Brasletti/Stealthmax_V2/Printable_Files/0_Chamber_Side_Mounting/CPAP_Intakes/CPAP_Tube_2020_Extrusion_Mount.stl

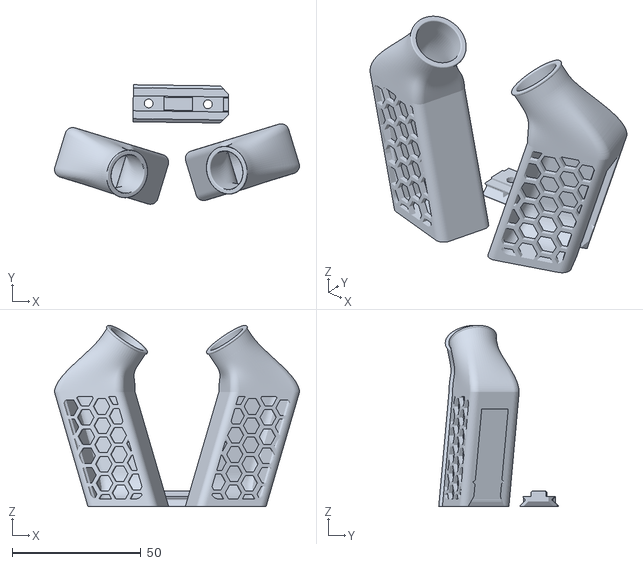
[picture p17: CAD file, 2025-04-10]
Printable_Files/0_Chamber_Side_Mounting/CPAP_Intakes/CPAP_Tube_2020_Extrusion_Mount.stl
95.1 x 46.4 x 70.4
