Brasletti/Stealthmax_V2/Printable_Files/1_Flow_Chamber/Bottom_Port_Options/5p_Microfit.step

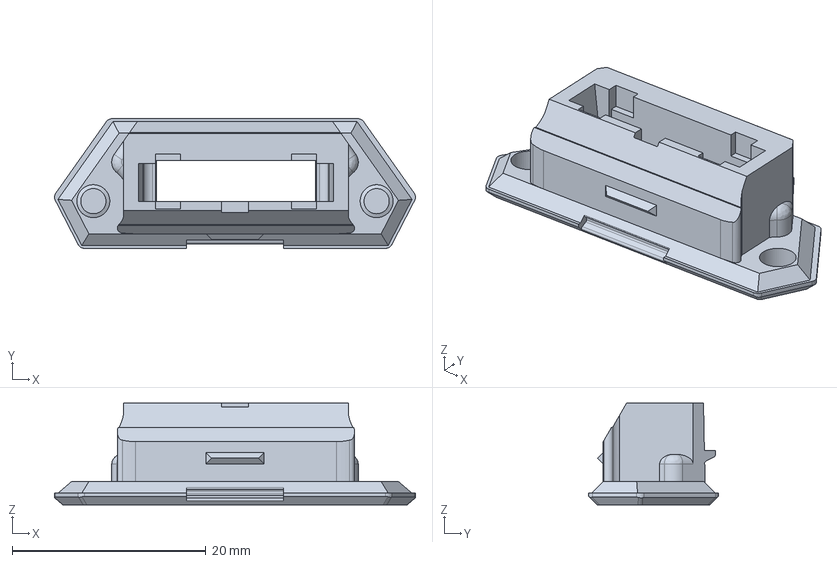
[picture p18: CAD file, 2025-04-05]
Printable_Files/1_Flow_Chamber/Bottom_Port_Options/5p_Microfit.step
37.2 x 13.4 x 10.5 mm
