Brasletti/Stealthmax_V2/Printable_Files/1_Flow_Chamber/Bowden_Tube_Intake_Options/Right/[RIGHT]Low_Blank_noLED_High_M6_PC4.step

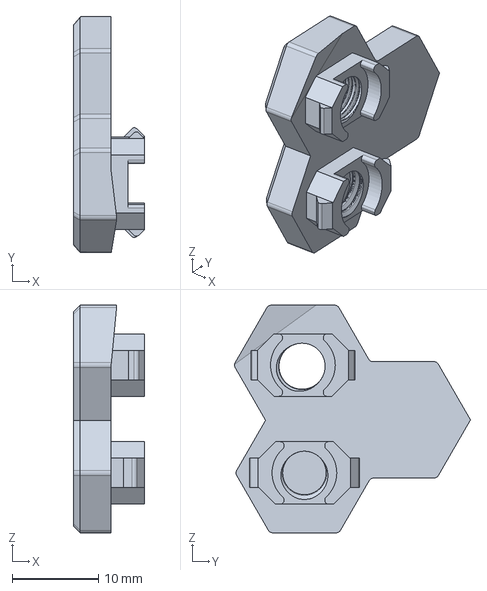
[picture p19: CAD file, 2025-04-05]
Printable_Files/1_Flow_Chamber/Bowden_Tube_Intake_Options/Right/[RIGHT]Low_Blank_noLED_High_M6_PC4.step
8.20 x 27.3 x 26.4 mm
