Brasletti/Stealthmax_V2/Printable_Files/1_Flow_Chamber/Bowden_Tube_Intake_Options/Standard_with_Single_PC6_Coupler.stl

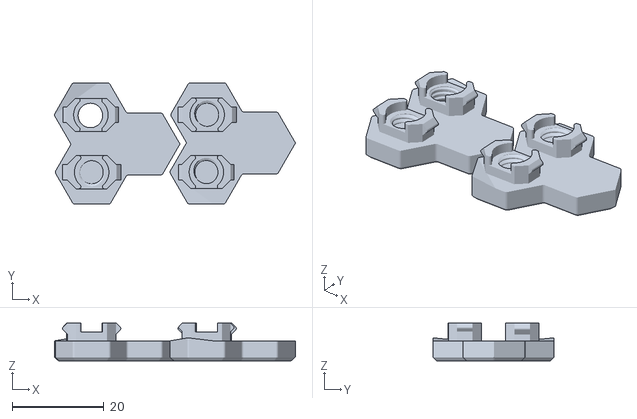
[picture p20: CAD file, 2025-03-30]
Printable_Files/1_Flow_Chamber/Bowden_Tube_Intake_Options/Standard_with_Single_PC6_Coupler.stl
52.5 x 26.4 x 8.20
