Brasletti/Stealthmax_V2/Printable_Files/0_Chamber_Side_Mounting/CPAP_Intakes/22mm_CPAP_Tube(LastZeanon)).step

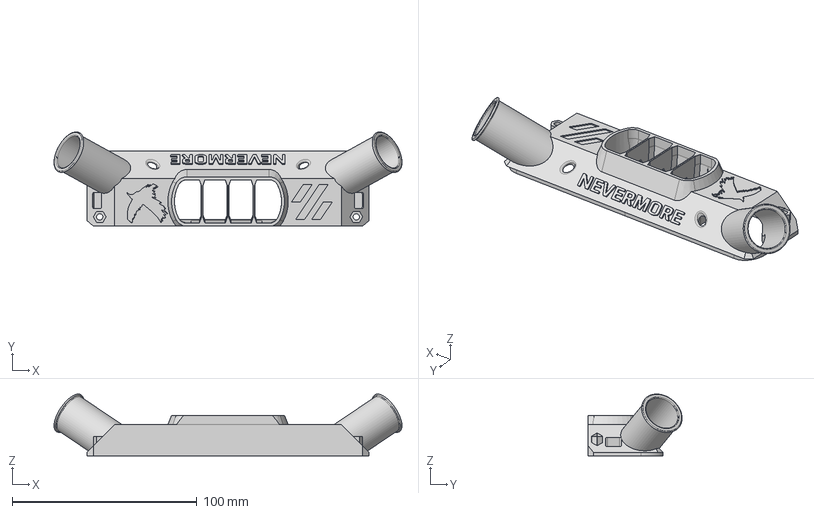
[picture p21: CAD file, 2025-04-05]
Printable_Files/0_Chamber_Side_Mounting/CPAP_Intakes/22mm_CPAP_Tube(LastZeanon)).step
188.4 x 51.0 x 33.5 mm
