Brasletti/Stealthmax_V2/Printable_Files/1_Flow_Chamber/Bottom_Port_Options/3p_Microfit.step

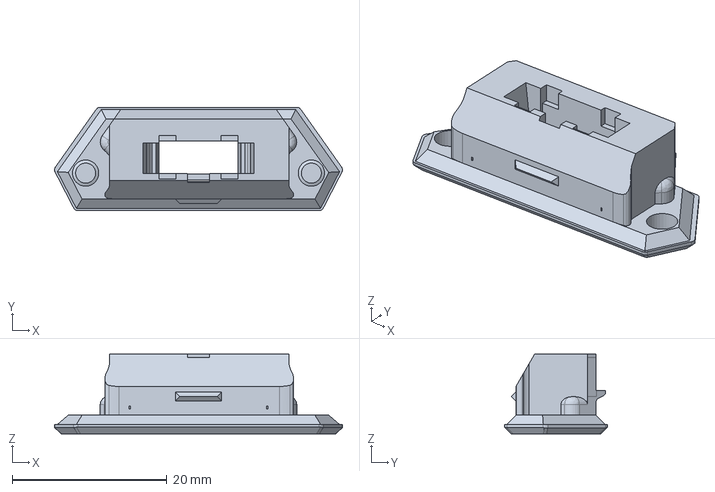
[picture p22: CAD file, 2025-04-05]
Printable_Files/1_Flow_Chamber/Bottom_Port_Options/3p_Microfit.step
37.3 x 13.4 x 10.3 mm
