Brasletti/Stealthmax_V2/Printable_Files/1_Flow_Chamber/Bottom_Port_Options/PC6_Bottom_Bowden.step

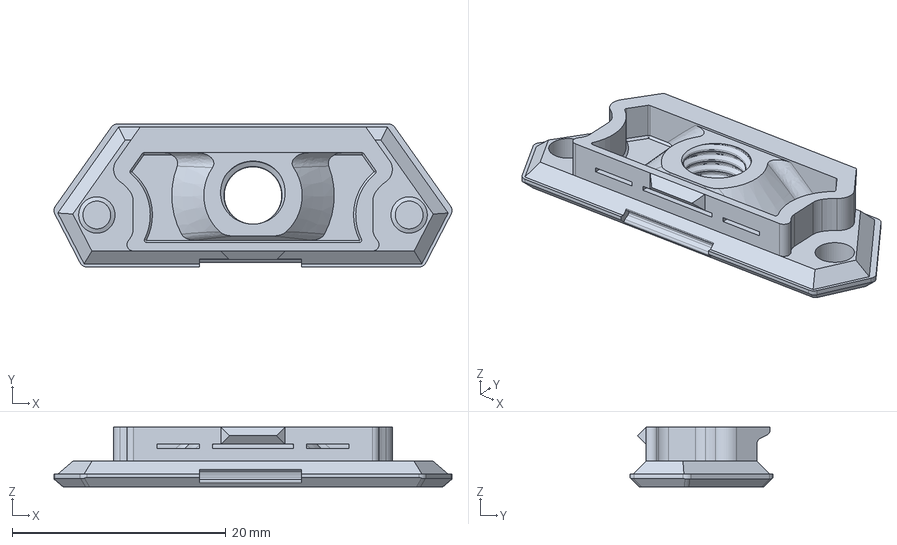
[picture p23: CAD file, 2025-04-05]
Printable_Files/1_Flow_Chamber/Bottom_Port_Options/PC6_Bottom_Bowden.step
37.2 x 13.4 x 5.61 mm
