Brasletti/Stealthmax_V2/Printable_Files/1_Flow_Chamber/Bottom_Port_Options/22mm_ID_CPAP_intake_tube.step

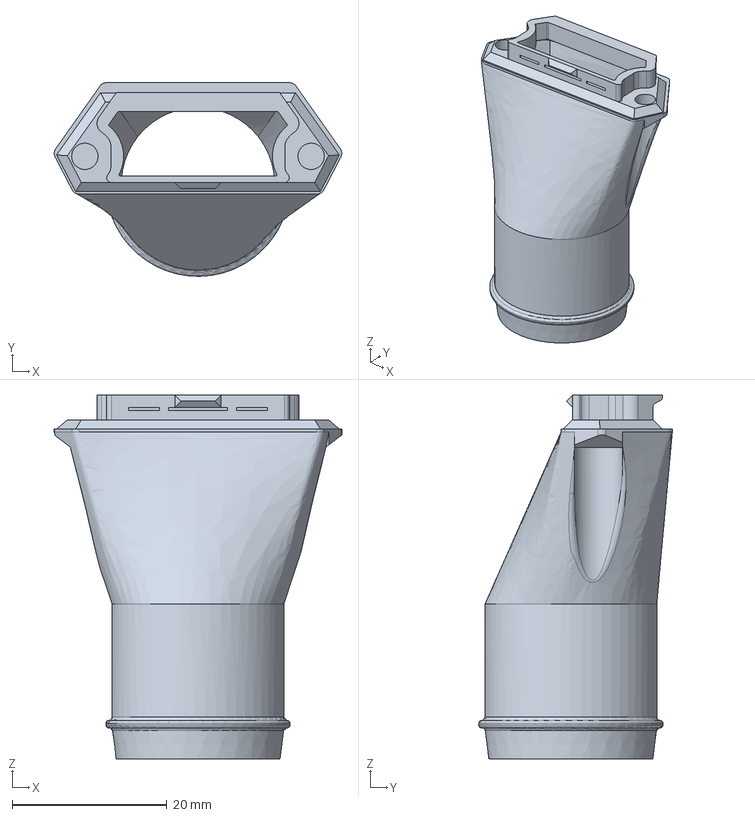
[picture p25: CAD file, 2025-04-05]
Printable_Files/1_Flow_Chamber/Bottom_Port_Options/22mm_ID_CPAP_intake_tube.step
37.1 x 25.0 x 47.0 mm
