Brasletti/Stealthmax_V2/Printable_Files/1_Flow_Chamber/Bowden_Tube_Intake_Options/Right/[RIGHT]Low_M6_PC4_LED_High_M6_PC4.step

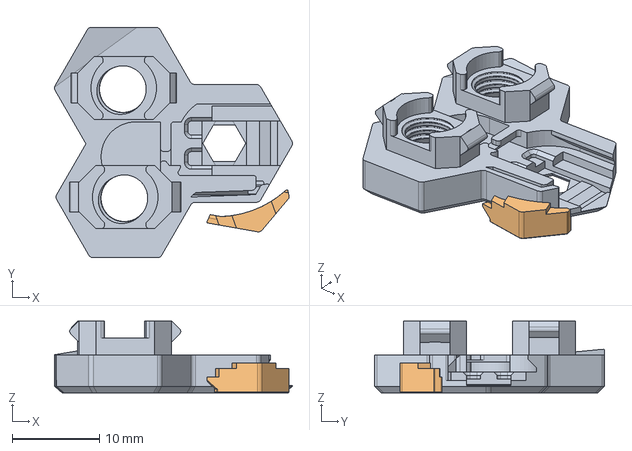
[picture p26: CAD file, 2025-04-05]
Printable_Files/1_Flow_Chamber/Bowden_Tube_Intake_Options/Right/[RIGHT]Low_M6_PC4_LED_High_M6_PC4.step
27.2 x 26.4 x 8.20 mm
