Brasletti/Stealthmax_V2/Printable_Files/1_Flow_Chamber/Bottom_Port_Options/Spare_Port.step

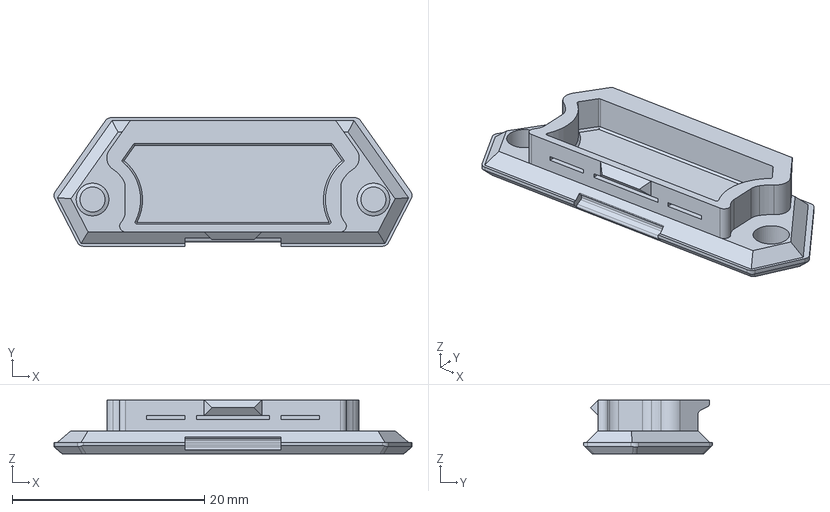
[picture p27: CAD file, 2025-04-05]
Printable_Files/1_Flow_Chamber/Bottom_Port_Options/Spare_Port.step
37.2 x 13.4 x 5.61 mm
