Brasletti/Stealthmax_V2/Printable_Files/1_Flow_Chamber/Bottom_Port_Options/17mm_ID_CPAP_intake_tube.step

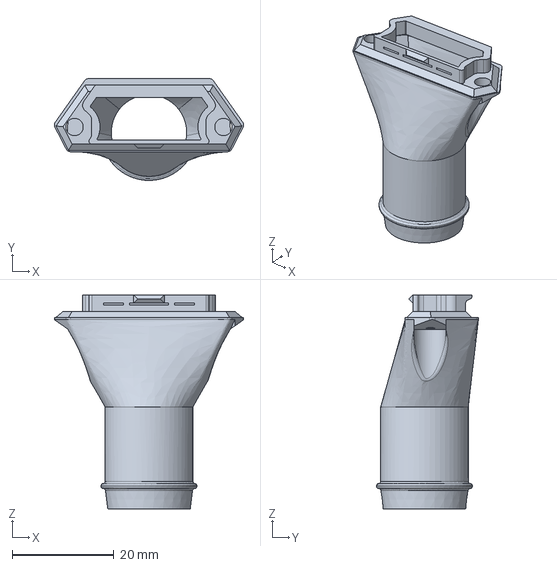
[picture p28: CAD file, 2025-04-05]
Printable_Files/1_Flow_Chamber/Bottom_Port_Options/17mm_ID_CPAP_intake_tube.step
37.1 x 20.0 x 42.0 mm
